ACKERMANNGUE/ACKERMANNGUE-AG_Dipl_Tech_2021_VoitureAssistee/code/Toolbox/Lidar/scanner/scan_room.png

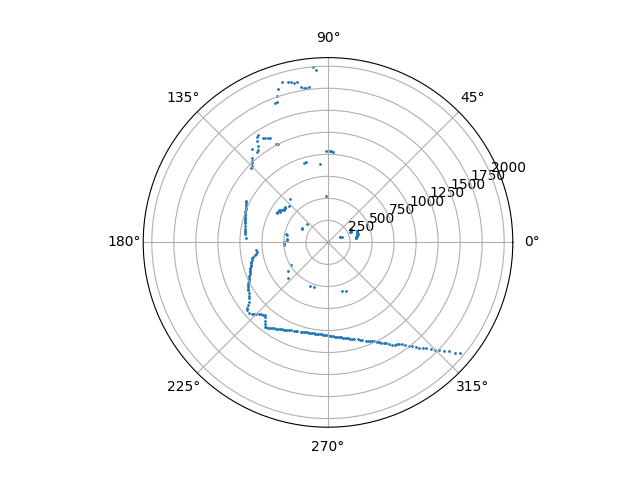
code/Toolbox/Lidar/scanner/scan_room.png
