ACKERMANNGUE/ACKERMANNGUE-AG_Dipl_Tech_2021_VoitureAssistee/code/Toolbox/OpenCV/shape_recognition/signs.png

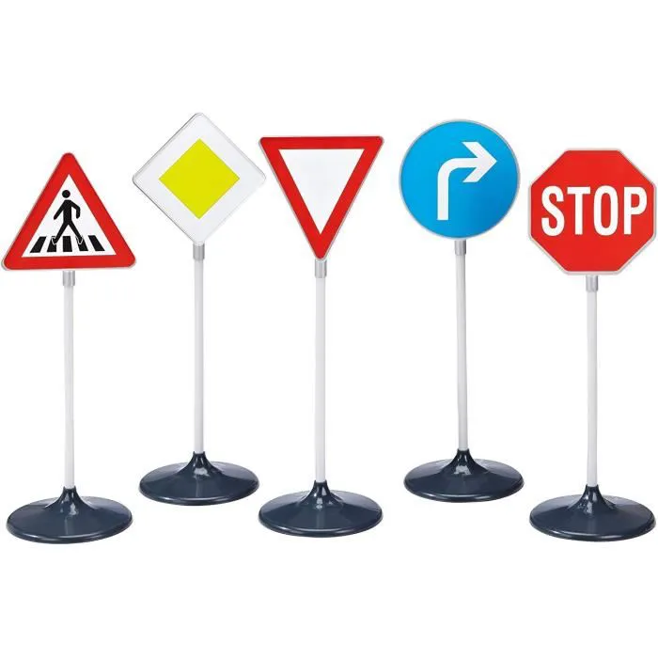
code/Toolbox/OpenCV/shape_recognition/signs.png
