ACKERMANNGUE/ACKERMANNGUE-AG_Dipl_Tech_2021_VoitureAssistee/docs/images/asus_wifi/router_branchement.jpg

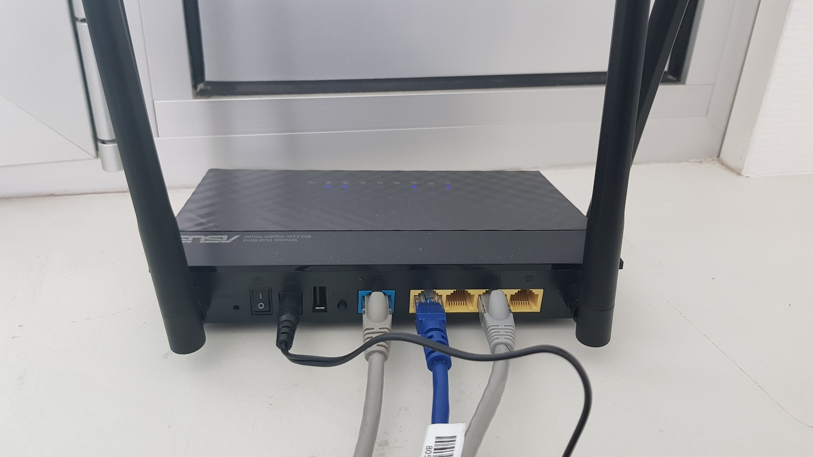
docs/images/asus_wifi/router_branchement.jpg
