ACKERMANNGUE/ACKERMANNGUE-AG_Dipl_Tech_2021_VoitureAssistee/docs/images/asus_wifi/router_leds_signification.jpg

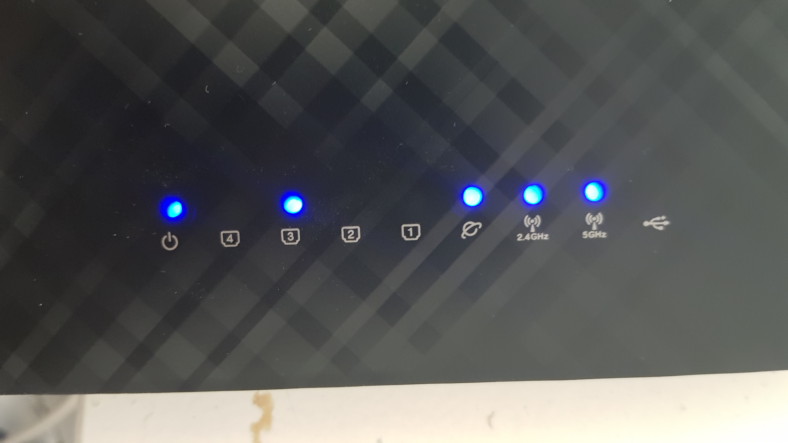
docs/images/asus_wifi/router_leds_signification.jpg
