ACKERMANNGUE/ACKERMANNGUE-AG_Dipl_Tech_2021_VoitureAssistee/docs/images/branchements/branchement_brightpi.jpg

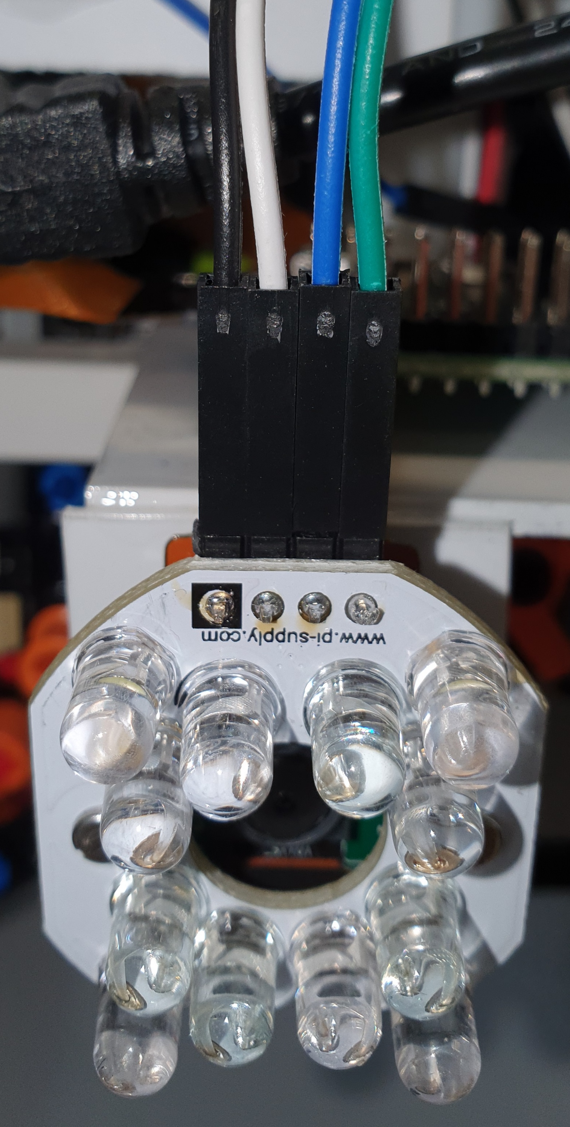
docs/images/branchements/branchement_brightpi.jpg
