ACKERMANNGUE/ACKERMANNGUE-AG_Dipl_Tech_2021_VoitureAssistee/docs/images/branchements/branchement_flyingfish.jpg

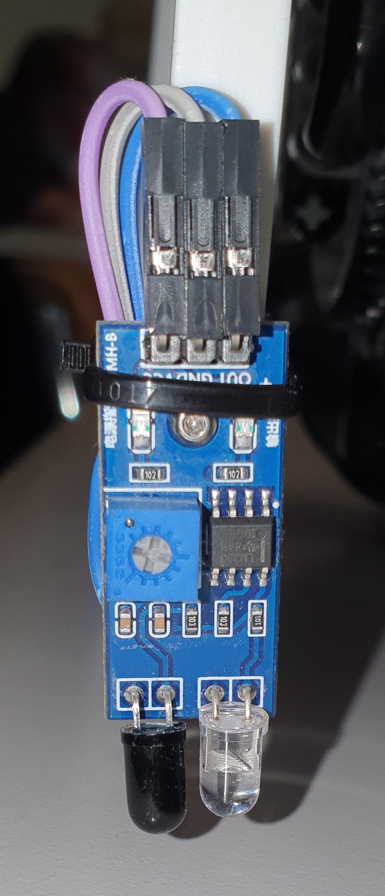
docs/images/branchements/branchement_flyingfish.jpg
