ACKERMANNGUE/ACKERMANNGUE-AG_Dipl_Tech_2021_VoitureAssistee/docs/images/branchements/rsp4_usb-c_1.jpg

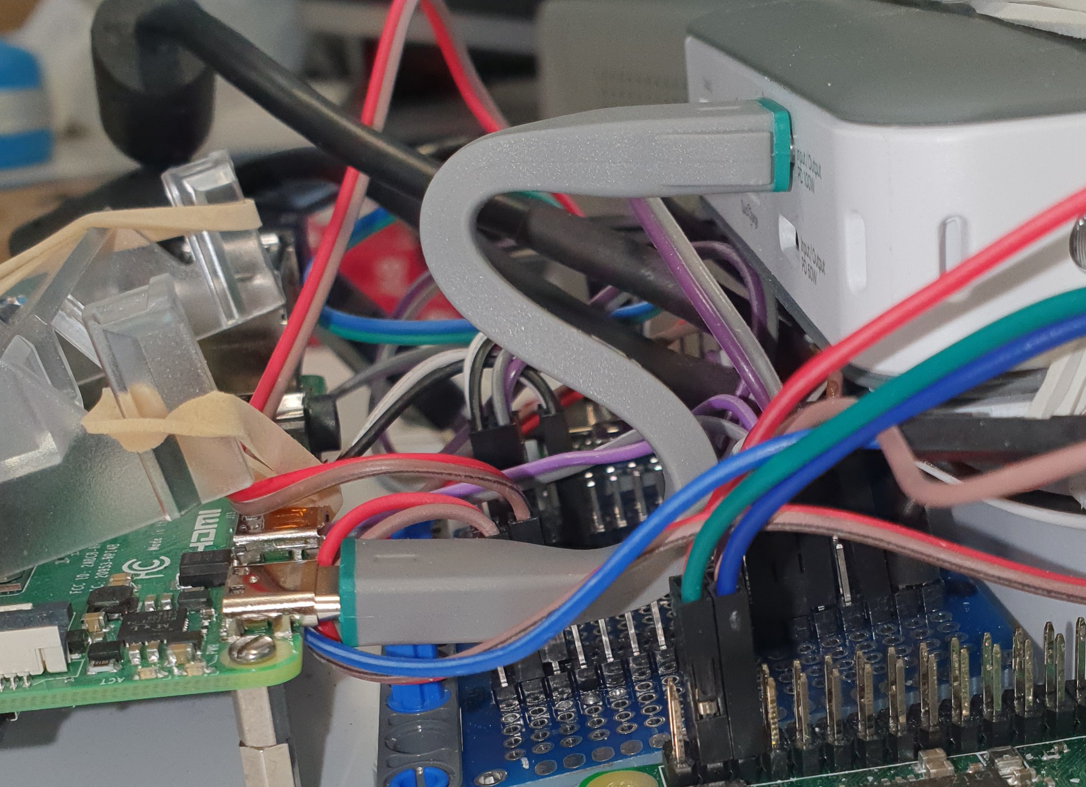
docs/images/branchements/rsp4_usb-c_1.jpg
