ACKERMANNGUE/ACKERMANNGUE-AG_Dipl_Tech_2021_VoitureAssistee/docs/images/branchements/rsp4_usb-c_2.jpg

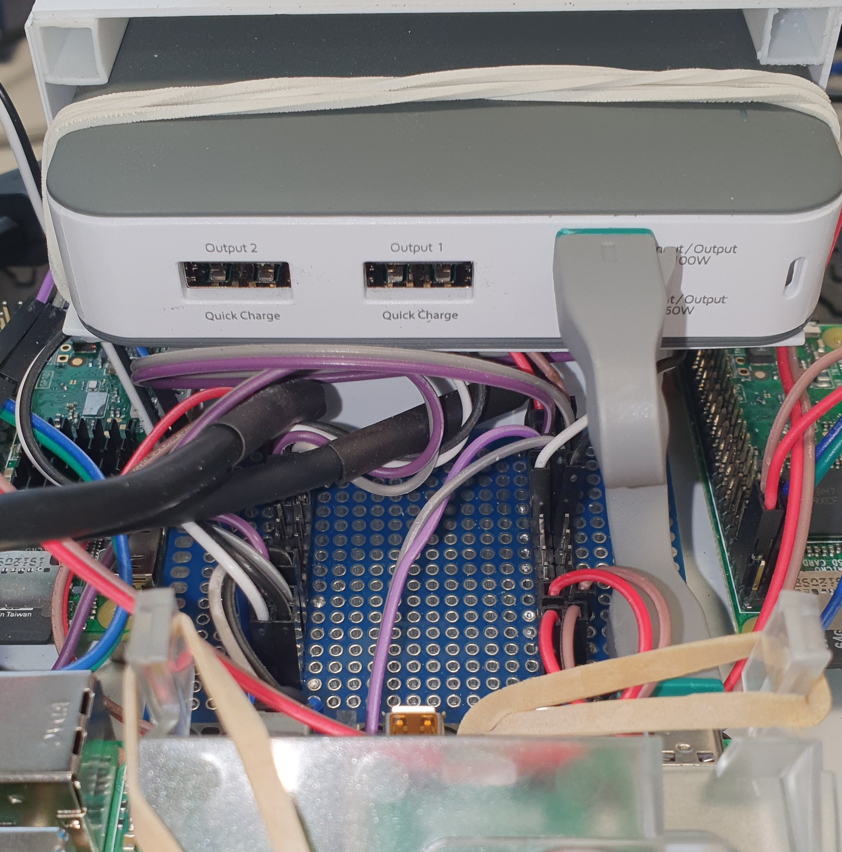
docs/images/branchements/rsp4_usb-c_2.jpg
