ACKERMANNGUE/ACKERMANNGUE-AG_Dipl_Tech_2021_VoitureAssistee/docs/images/clone_sd/balenaEtcher_clone_kingstone_SD_flash.png

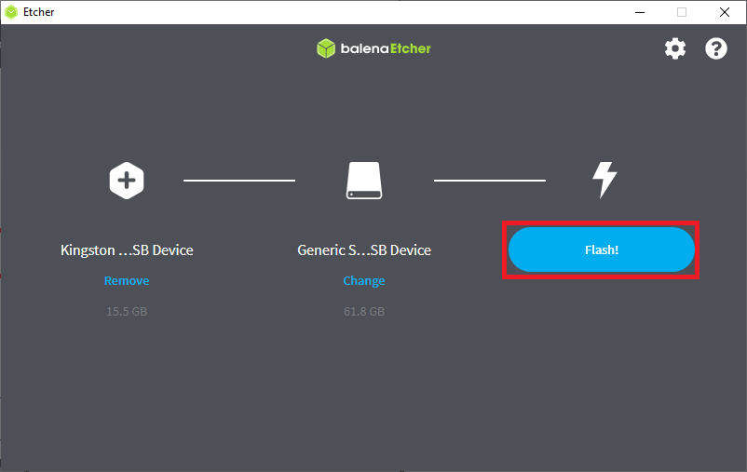
docs/images/clone_sd/balenaEtcher_clone_kingstone_SD_flash.png
