ACKERMANNGUE/ACKERMANNGUE-AG_Dipl_Tech_2021_VoitureAssistee/docs/images/clone_sd/balenaEtcher_clone_target.png

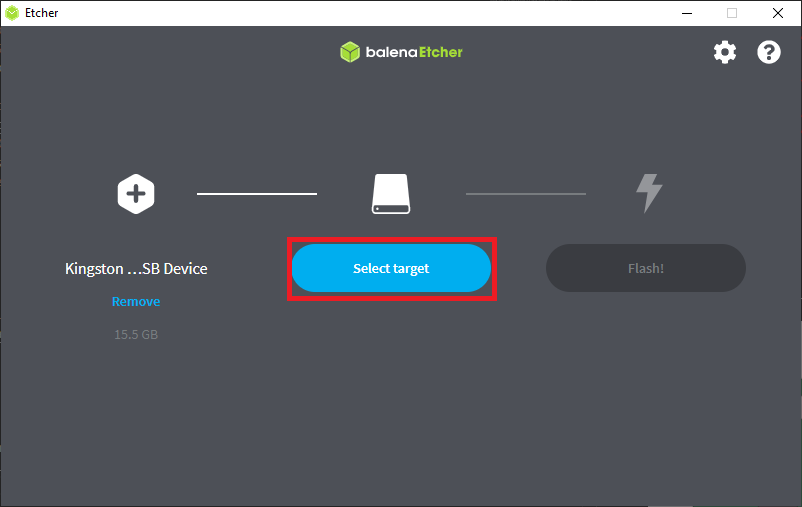
docs/images/clone_sd/balenaEtcher_clone_target.png
