ACKERMANNGUE/ACKERMANNGUE-AG_Dipl_Tech_2021_VoitureAssistee/docs/images/diag_classes/diag_class_carcontroller.png

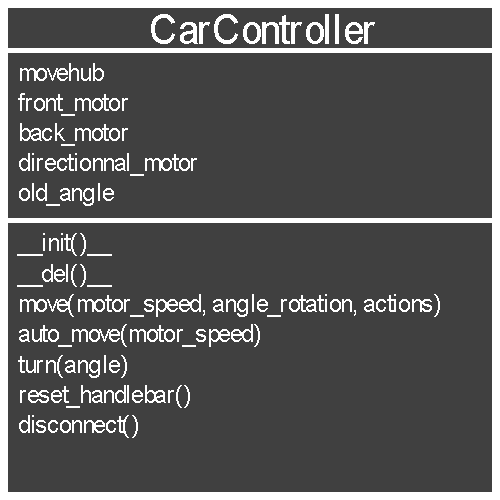
docs/images/diag_classes/diag_class_carcontroller.png
