ACKERMANNGUE/ACKERMANNGUE-AG_Dipl_Tech_2021_VoitureAssistee/docs/images/diag_routes_rsp0wifi_server.png

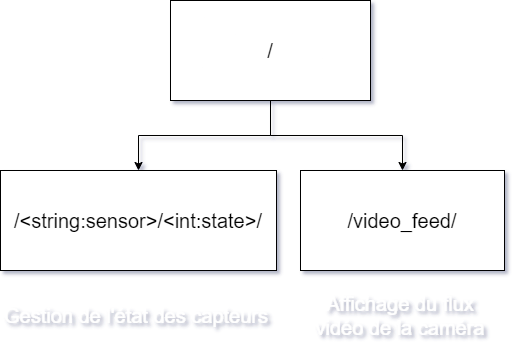
docs/images/diag_routes_rsp0wifi_server.png
