ACKERMANNGUE/ACKERMANNGUE-AG_Dipl_Tech_2021_VoitureAssistee/docs/images/diag_routes_rsp4_server.png

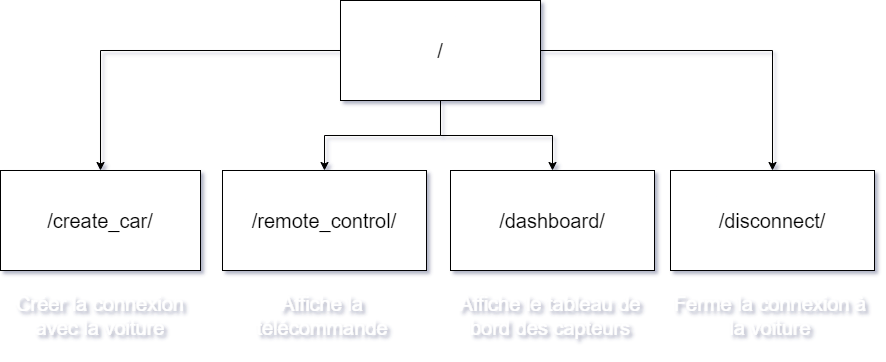
docs/images/diag_routes_rsp4_server.png
