ACKERMANNGUE/ACKERMANNGUE-AG_Dipl_Tech_2021_VoitureAssistee/docs/images/graph_lidar.gif

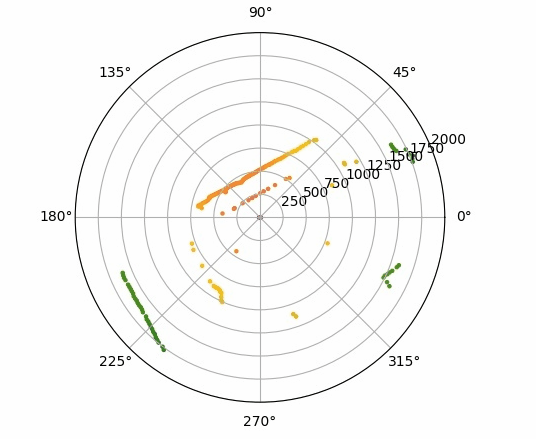
docs/images/graph_lidar.gif
