ACKERMANNGUE/ACKERMANNGUE-AG_Dipl_Tech_2021_VoitureAssistee/docs/images/raspap/ui_dashboard_hotspot_security.png

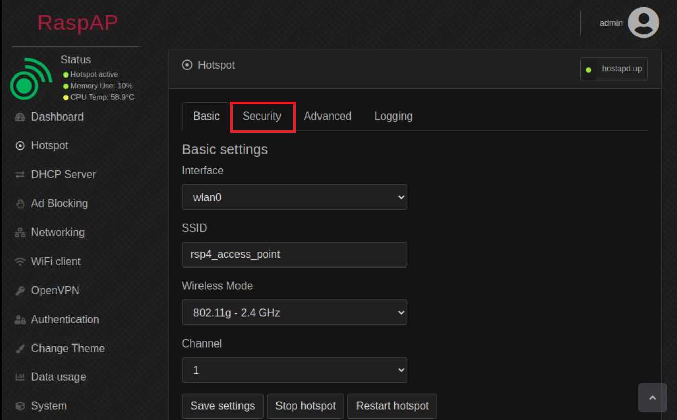
docs/images/raspap/ui_dashboard_hotspot_security.png
