ACKERMANNGUE/ACKERMANNGUE-AG_Dipl_Tech_2021_VoitureAssistee/docs/images/raspberrys/pi0_wifi.jpg

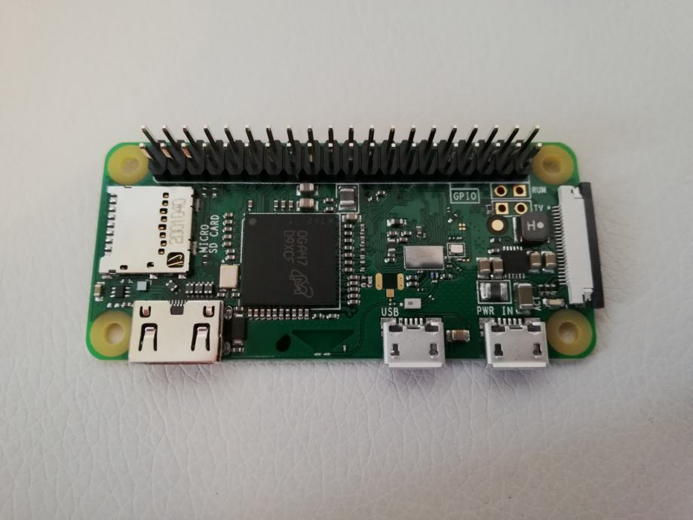
docs/images/raspberrys/pi0_wifi.jpg
