ACKERMANNGUE/ACKERMANNGUE-AG_Dipl_Tech_2021_VoitureAssistee/docs/images/raspberrys/rsp0wifi_schema.png

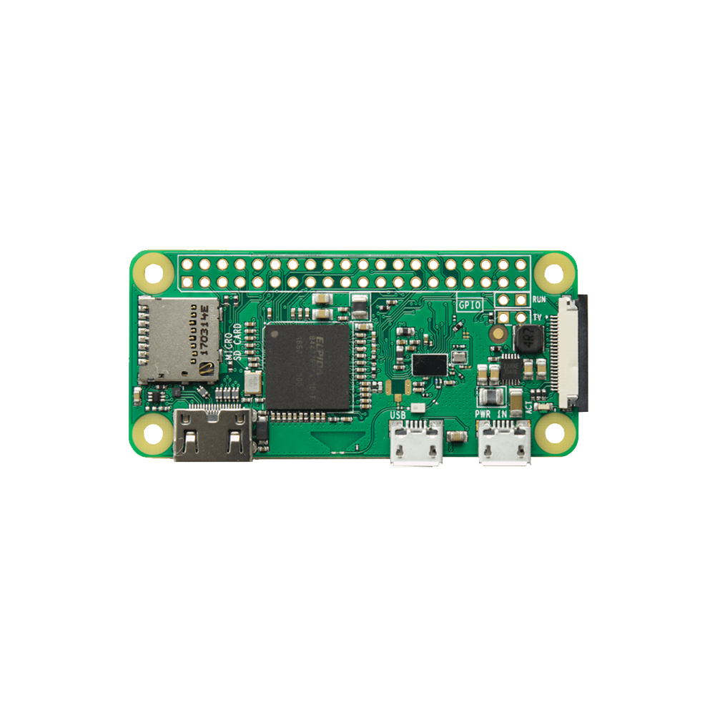
docs/images/raspberrys/rsp0wifi_schema.png
