ACKERMANNGUE/ACKERMANNGUE-AG_Dipl_Tech_2021_VoitureAssistee/docs/images/references_poster/ag_sensors.png

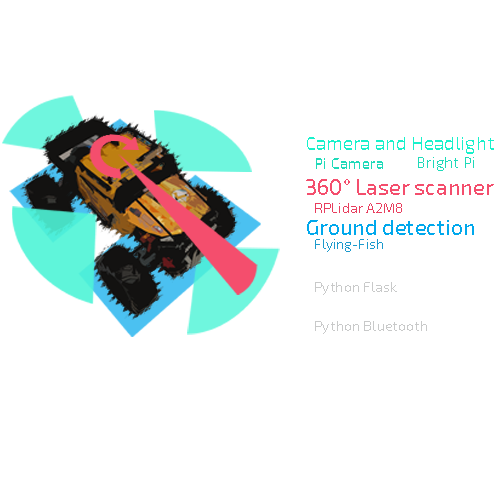
docs/images/references_poster/ag_sensors.png
