ACKERMANNGUE/ACKERMANNGUE-AG_Dipl_Tech_2021_VoitureAssistee/docs/images/references_poster/ag_technos.png

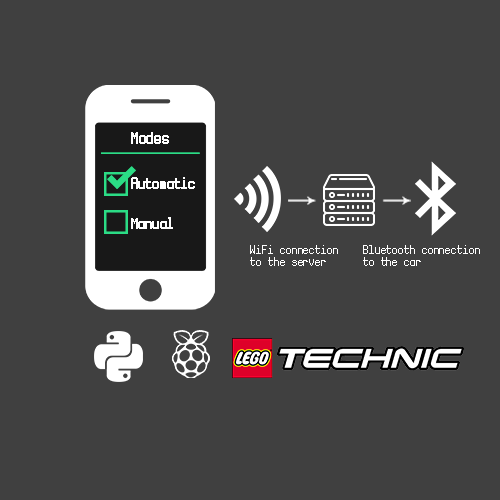
docs/images/references_poster/ag_technos.png
