ACKERMANNGUE/ACKERMANNGUE-AG_Dipl_Tech_2021_VoitureAssistee/docs/images/references_poster/croquis_poster.jpg

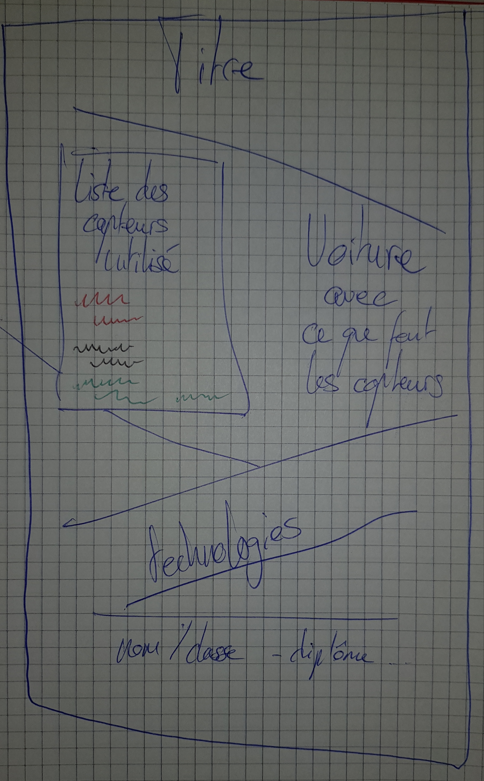
docs/images/references_poster/croquis_poster.jpg
