ACKERMANNGUE/ACKERMANNGUE-AG_Dipl_Tech_2021_VoitureAssistee/docs/images/references_poster/Elegant-Road-Sand-texture-.jpg

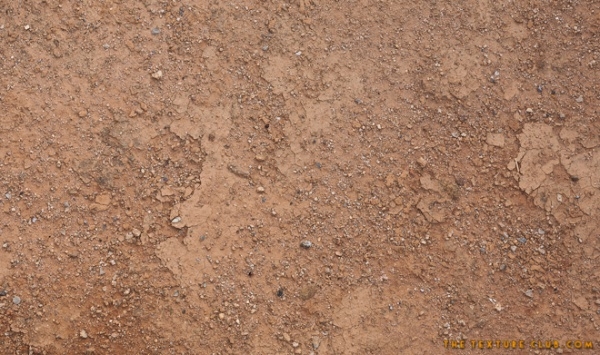
docs/images/references_poster/Elegant-Road-Sand-texture-.jpg
