ACKERMANNGUE/ACKERMANNGUE-AG_Dipl_Tech_2021_VoitureAssistee/docs/images/references_poster/voiture.jpg

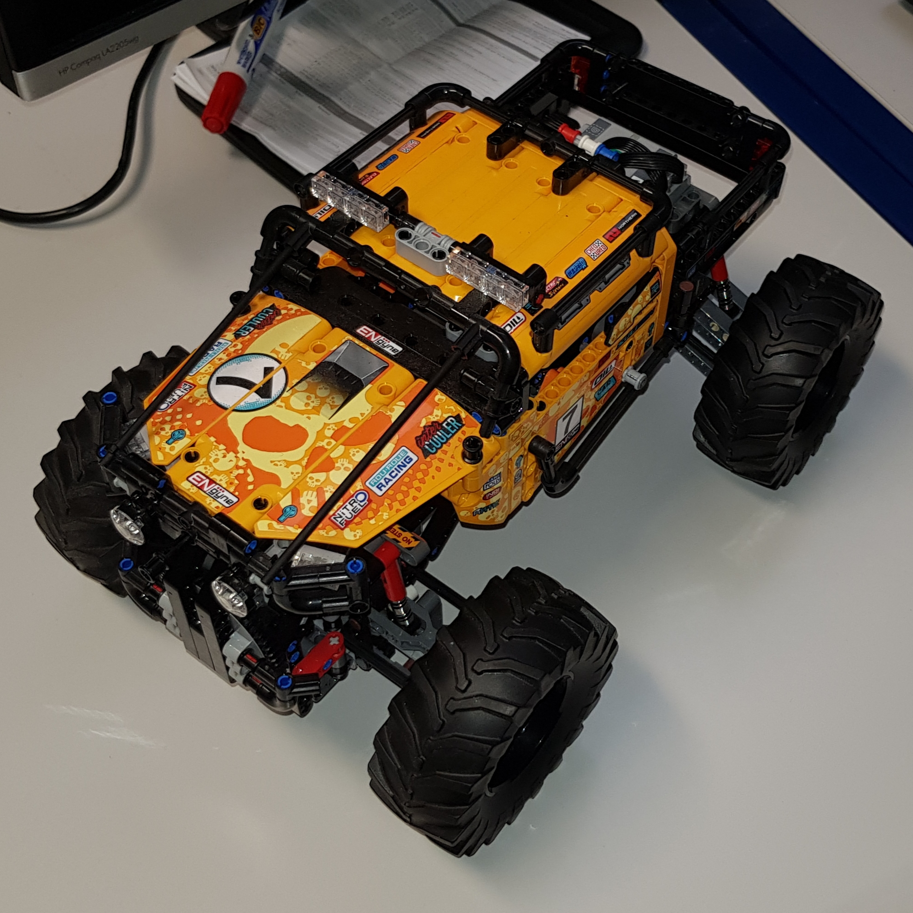
docs/images/references_poster/voiture.jpg
