ACKERMANNGUE/ACKERMANNGUE-AG_Dipl_Tech_2021_VoitureAssistee/docs/images/schema/3ccb0c7c-8111-4046-9295-0e27cd589b31.jpg

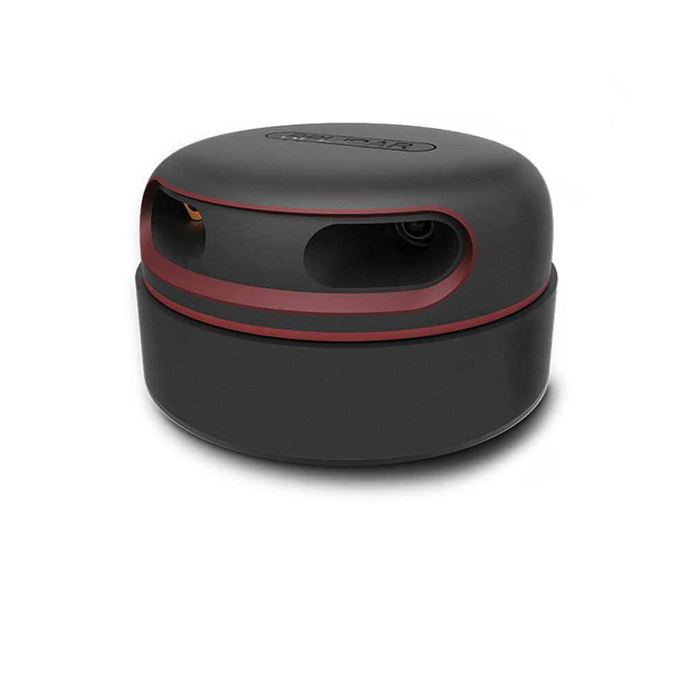
docs/images/schema/3ccb0c7c-8111-4046-9295-0e27cd589b31.jpg
