ACKERMANNGUE/ACKERMANNGUE-AG_Dipl_Tech_2021_VoitureAssistee/docs/images/schema/algo_recup_donnees_lidar.png

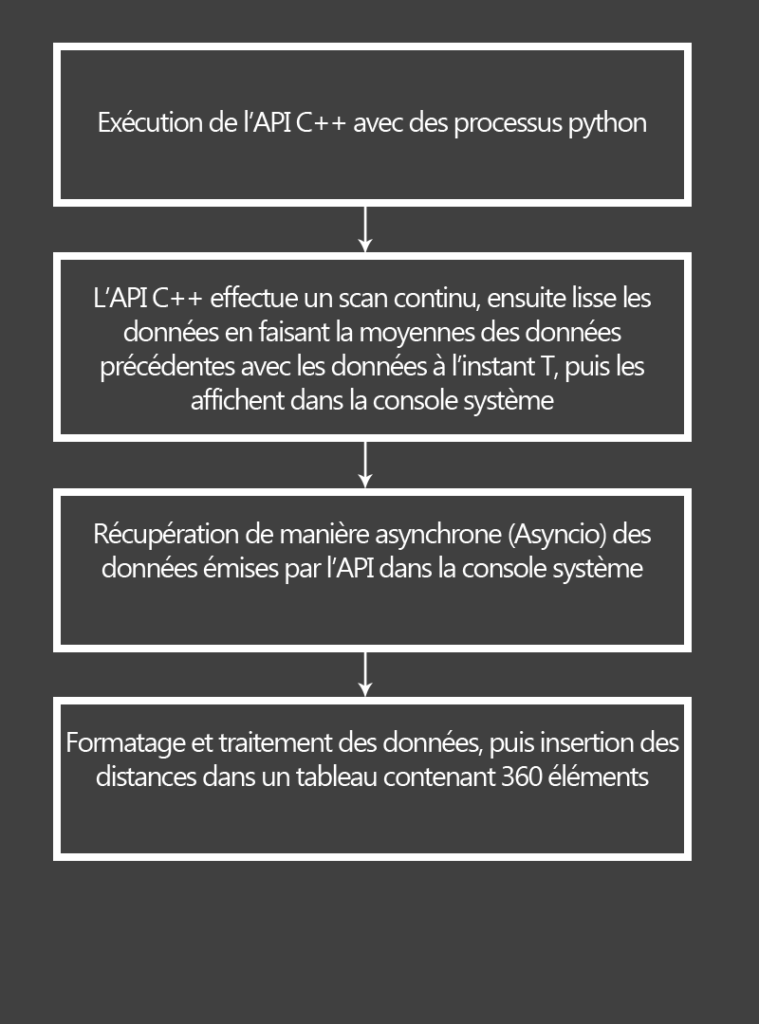
docs/images/schema/algo_recup_donnees_lidar.png
