ACKERMANNGUE/ACKERMANNGUE-AG_Dipl_Tech_2021_VoitureAssistee/docs/images/schema/plan_voiture_presentation.png

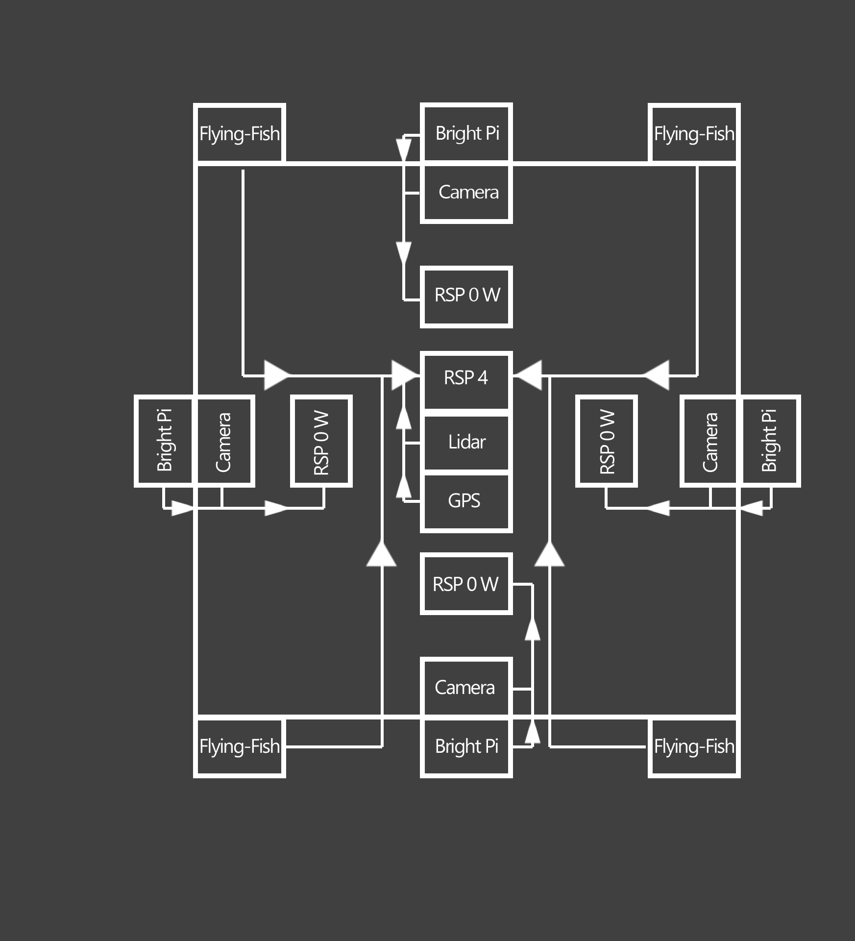
docs/images/schema/plan_voiture_presentation.png
