ACKERMANNGUE/ACKERMANNGUE-AG_Dipl_Tech_2021_VoitureAssistee/docs/images/schema/routes_serveur_principal.png

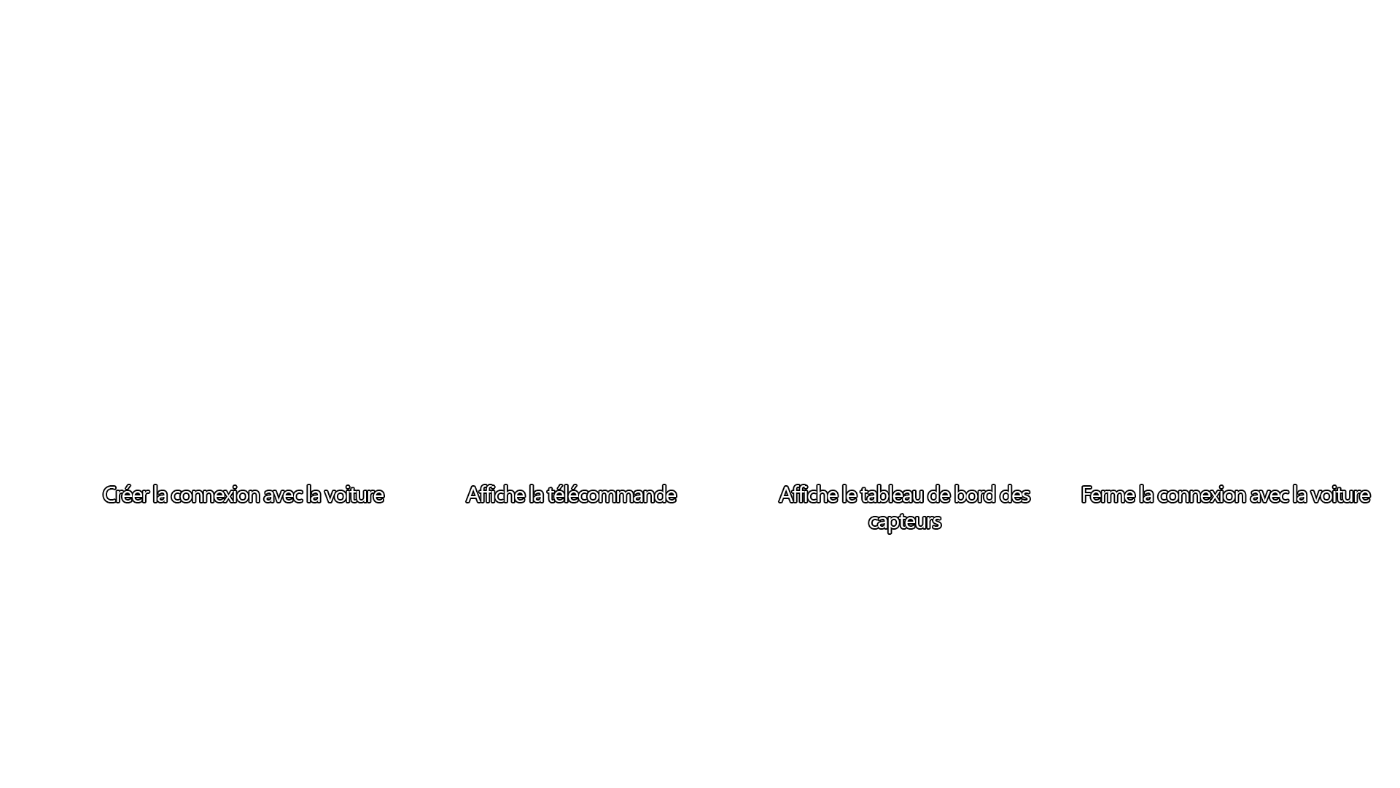
docs/images/schema/routes_serveur_principal.png
