ACKERMANNGUE/ACKERMANNGUE-AG_Dipl_Tech_2021_VoitureAssistee/docs/images/schema/routes_serveur_secondaires.png

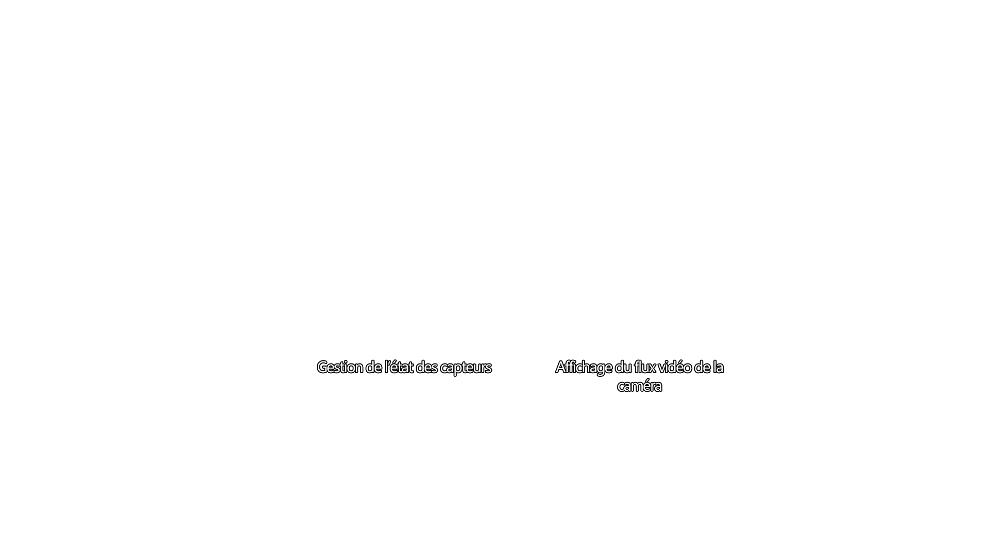
docs/images/schema/routes_serveur_secondaires.png
