ACKERMANNGUE/ACKERMANNGUE-AG_Dipl_Tech_2021_VoitureAssistee/docs/images/schema/serial_lidar.jpg

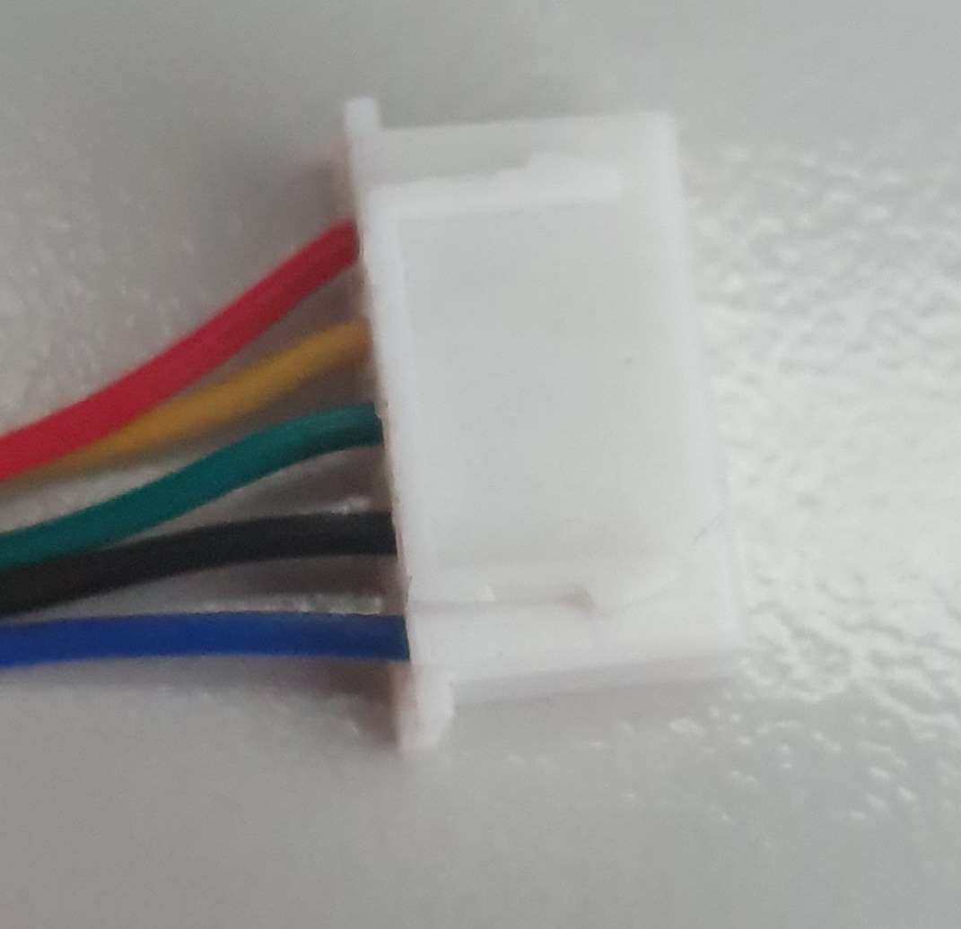
docs/images/schema/serial_lidar.jpg
