ACKERMANNGUE/ACKERMANNGUE-AG_Dipl_Tech_2021_VoitureAssistee/docs/images/technic_hub/blink_blue.png

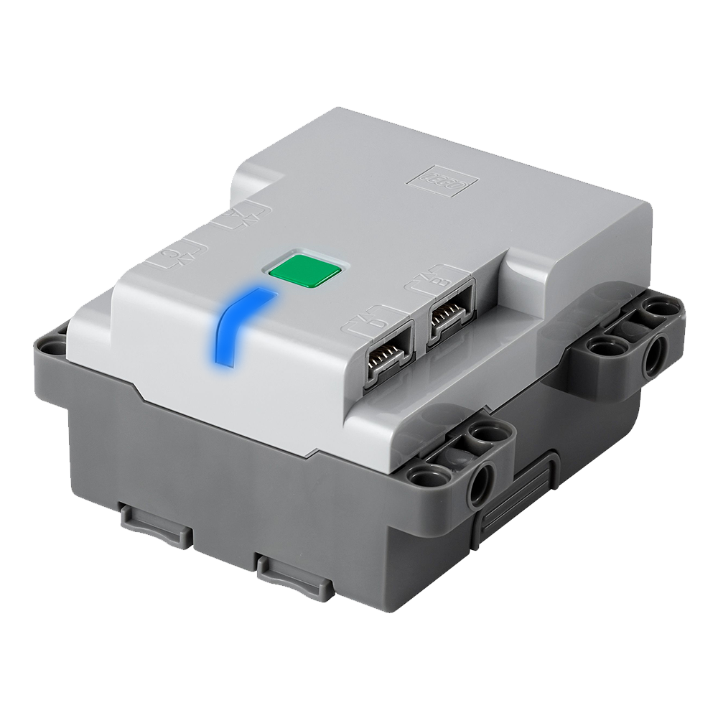
docs/images/technic_hub/blink_blue.png
