ACKERMANNGUE/ACKERMANNGUE-AG_Dipl_Tech_2021_VoitureAssistee/docs/images/technic_hub/hub.jpg

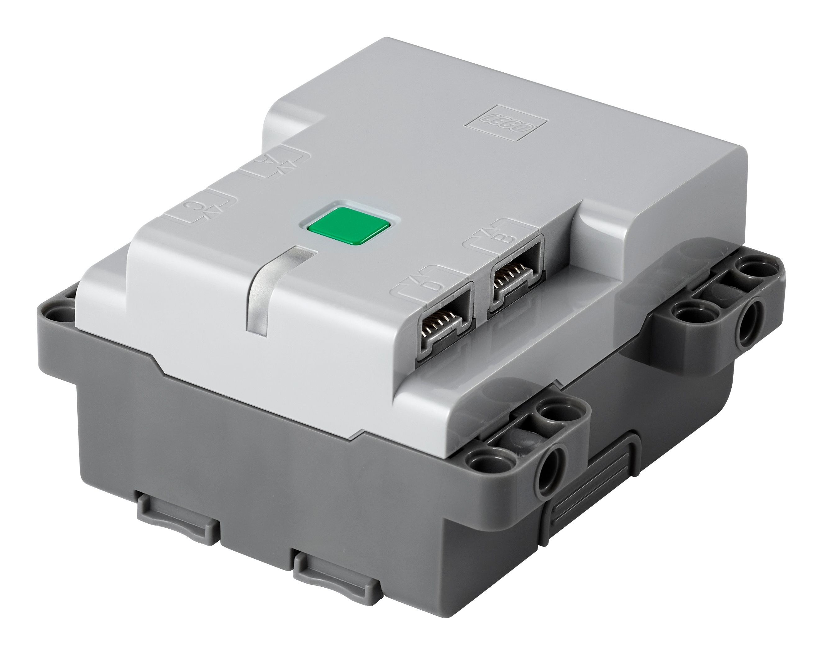
docs/images/technic_hub/hub.jpg
