ACKERMANNGUE/ACKERMANNGUE-AG_Dipl_Tech_2021_VoitureAssistee/docs/images/voiture/voiture_bord_de_table_extreme_2.jpg

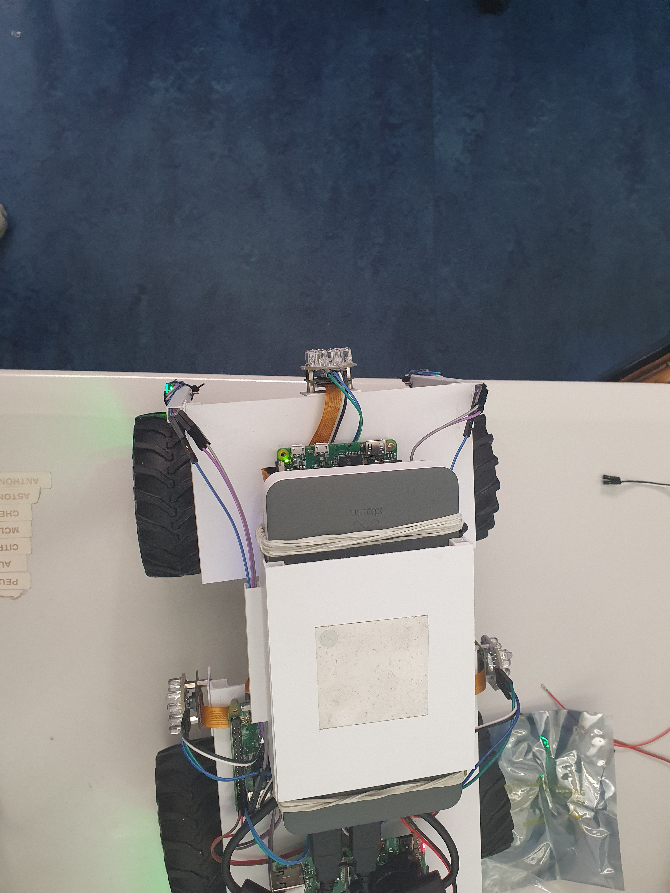
docs/images/voiture/voiture_bord_de_table_extreme_2.jpg
