ACKERMANNGUE/ACKERMANNGUE-AG_Dipl_Tech_2021_VoitureAssistee/docs/images/voiture/voiture_bord_de_table_extreme_3.jpg

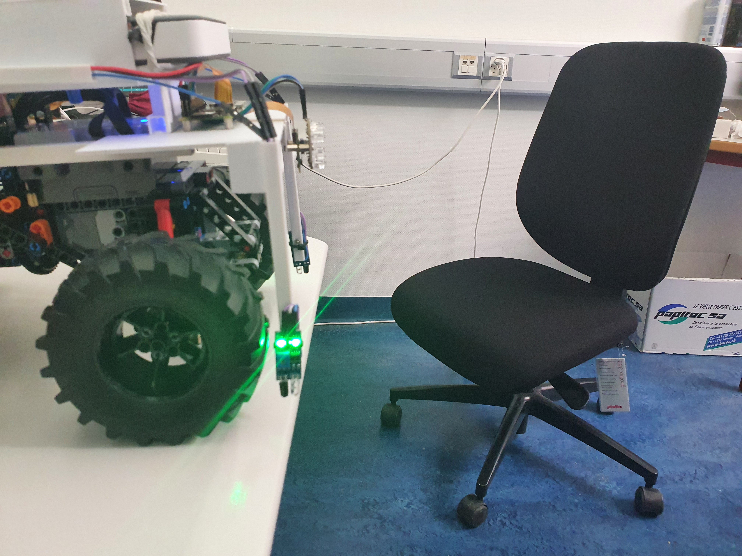
docs/images/voiture/voiture_bord_de_table_extreme_3.jpg
