ACKERMANNGUE/ACKERMANNGUE-AG_Dipl_Tech_2021_VoitureAssistee/docs/images/voiture/voiture_cablage_1.jpg

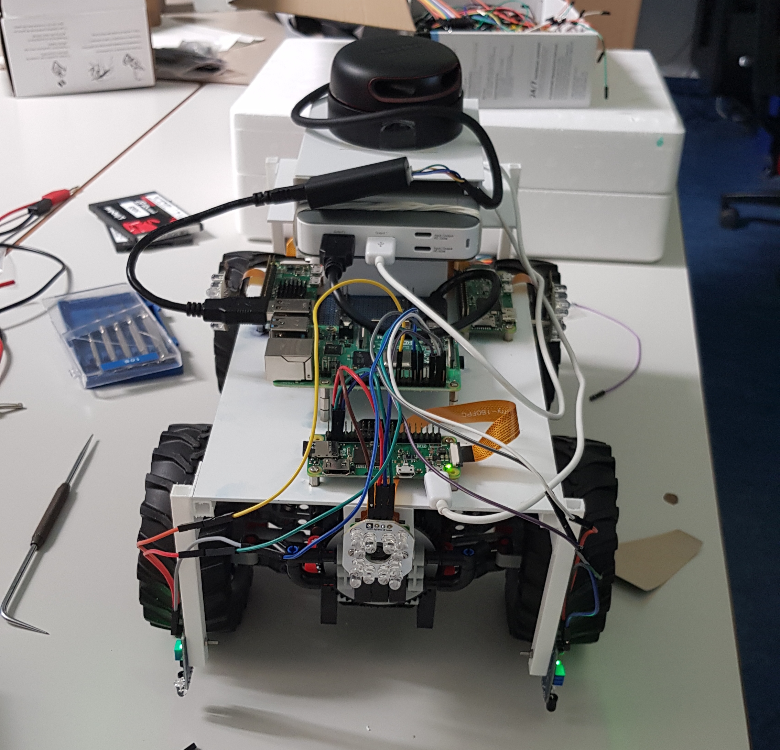
docs/images/voiture/voiture_cablage_1.jpg
