ACKERMANNGUE/ACKERMANNGUE-AG_Dipl_Tech_2021_VoitureAssistee/docs/images/voiture/voiture_cablage_2.jpg

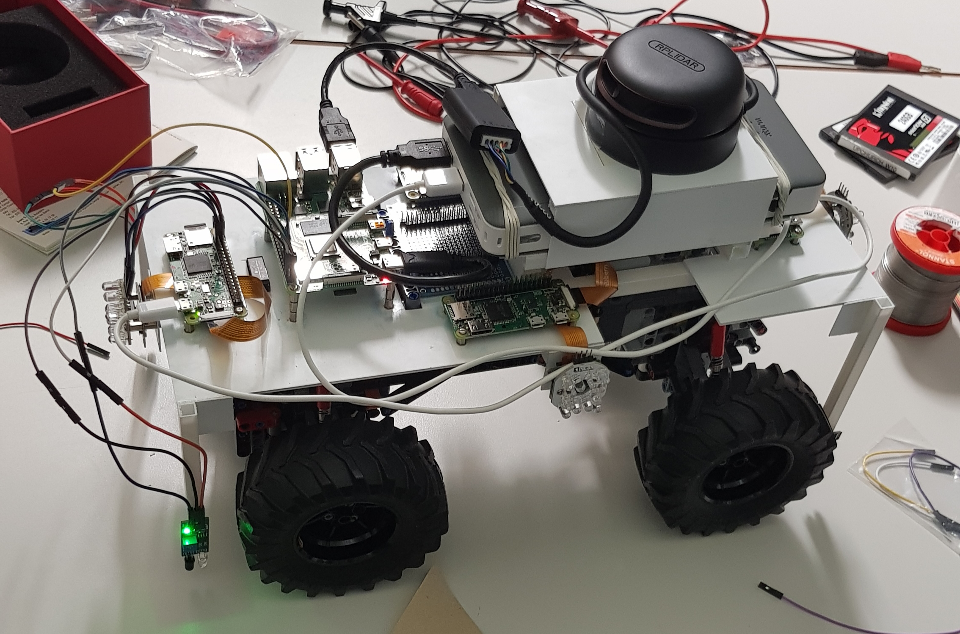
docs/images/voiture/voiture_cablage_2.jpg
