ACKERMANNGUE/ACKERMANNGUE-AG_Dipl_Tech_2021_VoitureAssistee/docs/images/voiture/voiture_vue_du_cote_arriere.jpg

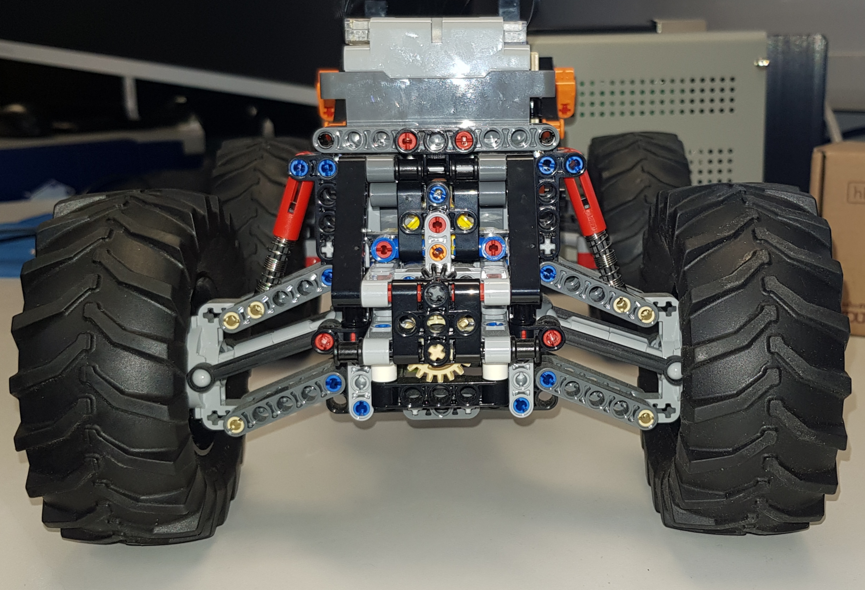
docs/images/voiture/voiture_vue_du_cote_arriere.jpg
