ACKERMANNGUE/ACKERMANNGUE-AG_Dipl_Tech_2021_VoitureAssistee/docs/images/voiture/voiture_vue_du_dessus.jpg

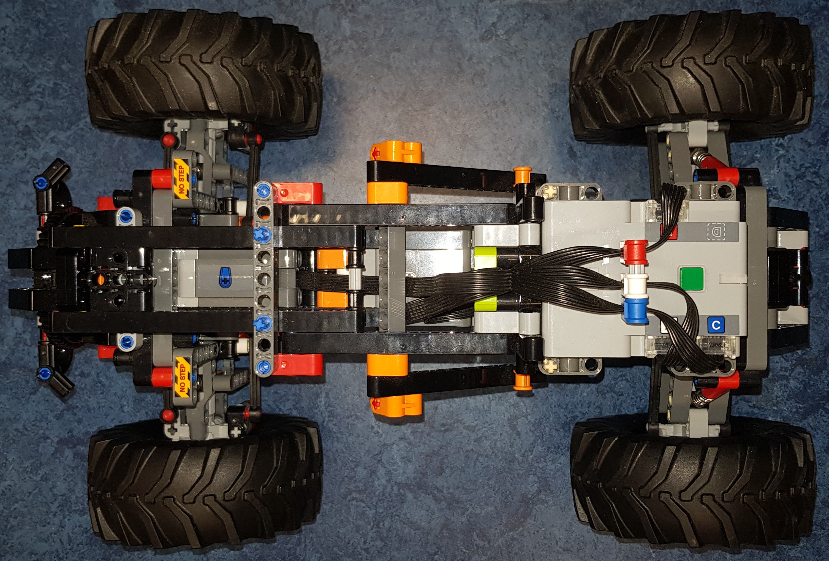
docs/images/voiture/voiture_vue_du_dessus.jpg
