ACKERMANNGUE/ACKERMANNGUE-AG_Dipl_Tech_2021_VoitureAssistee/site/images/gatt/EFR_Connect_TechnicHub.jpg

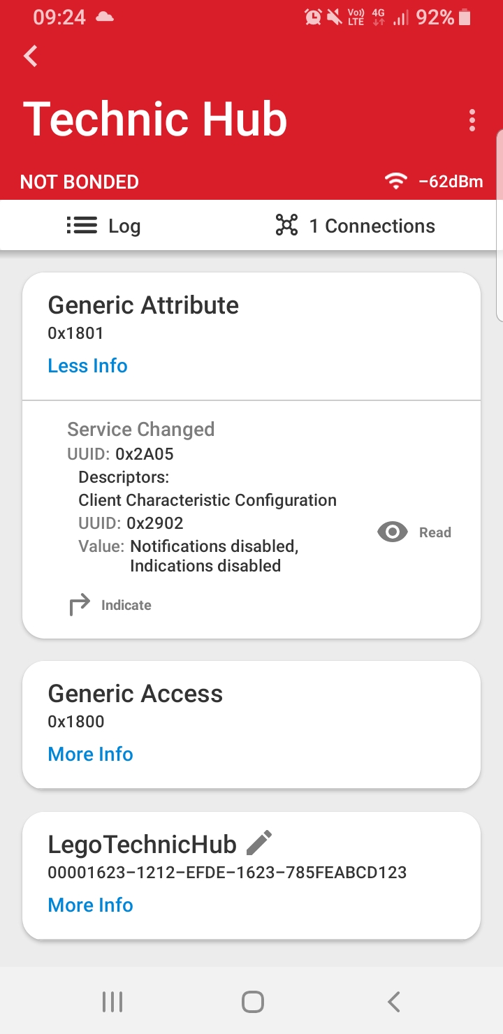
site/images/gatt/EFR_Connect_TechnicHub.jpg
