ACKERMANNGUE/ACKERMANNGUE-AG_Dipl_Tech_2021_VoitureAssistee/site/images/lidar/20210427_124223.jpg

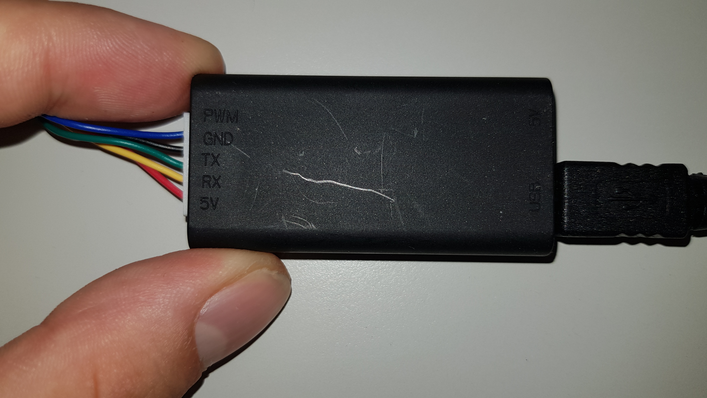
site/images/lidar/20210427_124223.jpg
