ACKERMANNGUE/ACKERMANNGUE-AG_Dipl_Tech_2021_VoitureAssistee/code/Toolbox/Lidar/scanner/test.png

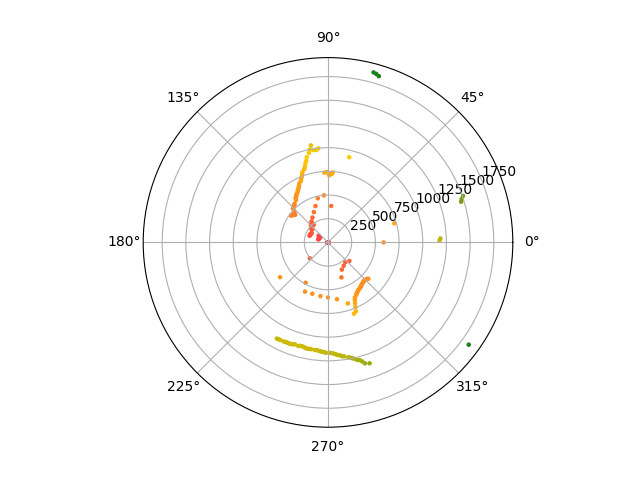
code/Toolbox/Lidar/scanner/test.png
